EstebanValverde/Holeboard/photos/IMG_20231107_094529.jpg

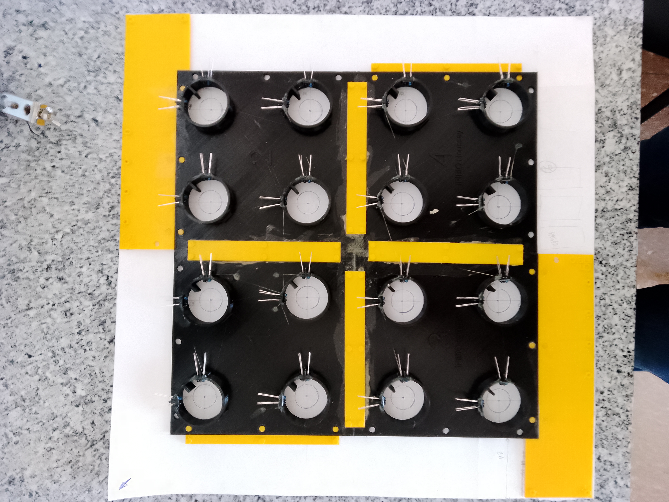
photos/IMG_20231107_094529.jpg
