EstebanValverde/Holeboard/photos/IMG_20231107_094548.jpg

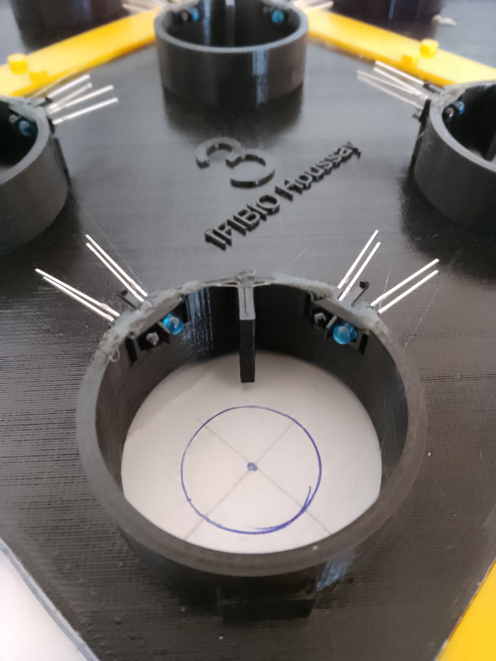
photos/IMG_20231107_094548.jpg
