EstebanValverde/Holeboard/photos/IMG_20231117_153157.jpg

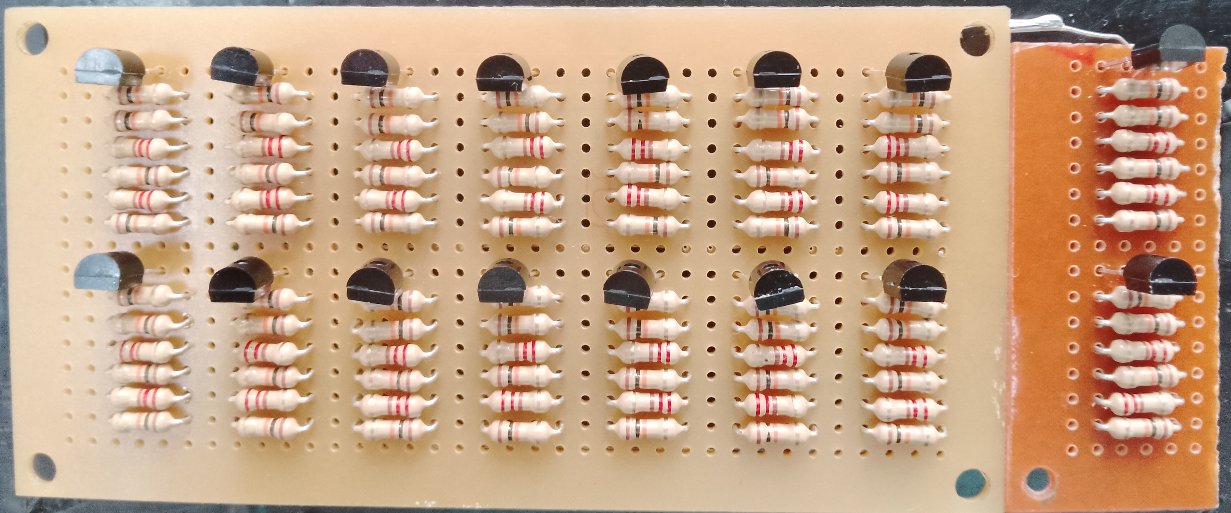
photos/IMG_20231117_153157.jpg
