EstebanValverde/Holeboard/photos/IMG_20231219_103728.jpg

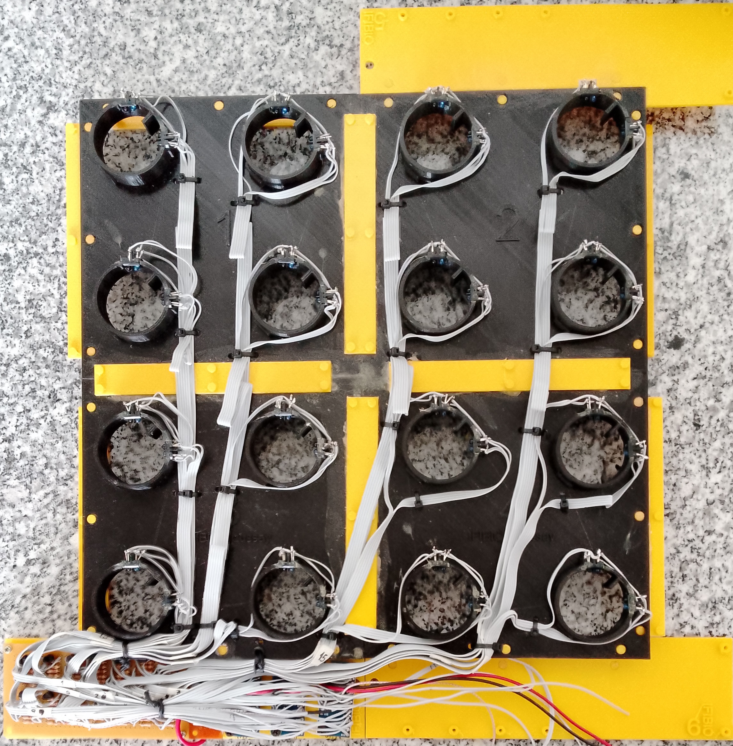
photos/IMG_20231219_103728.jpg
