EstebanValverde/Holeboard/photos/IMG_20231227_120412.jpg

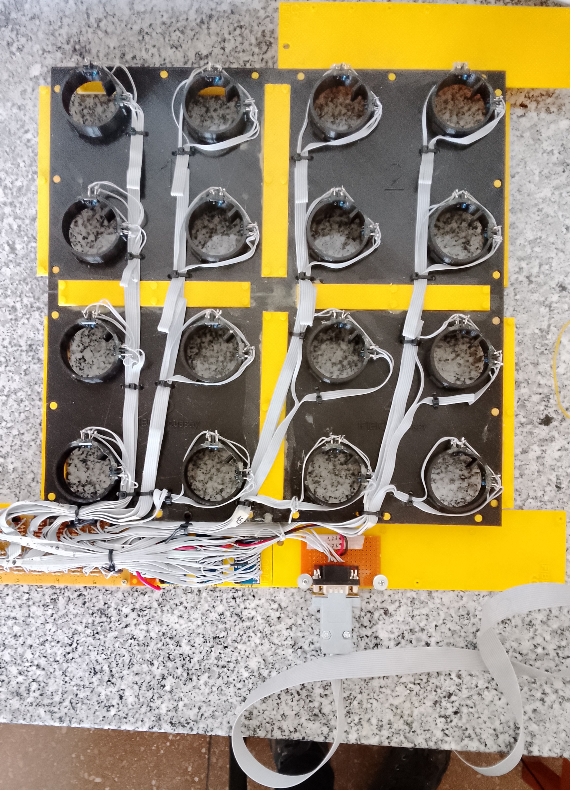
photos/IMG_20231227_120412.jpg
