EstebanValverde/Holeboard/photos/IMG_20240117_093414.jpg

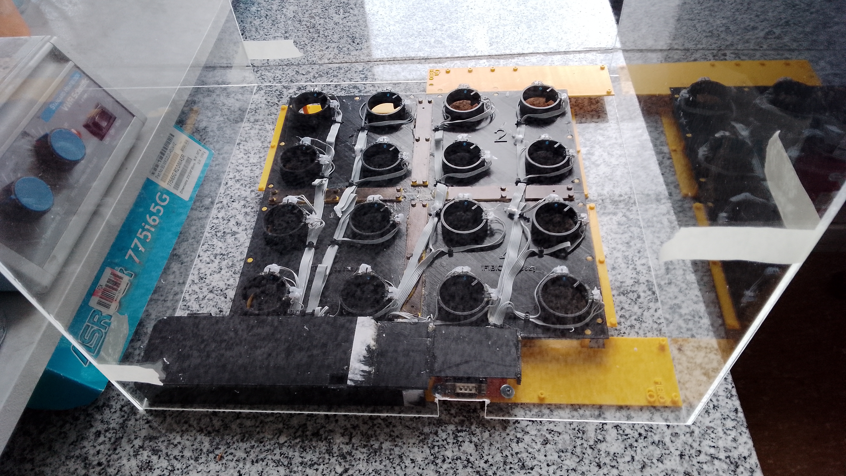
photos/IMG_20240117_093414.jpg
