EstebanValverde/Holeboard/photos/IMG_20240117_093420.jpg

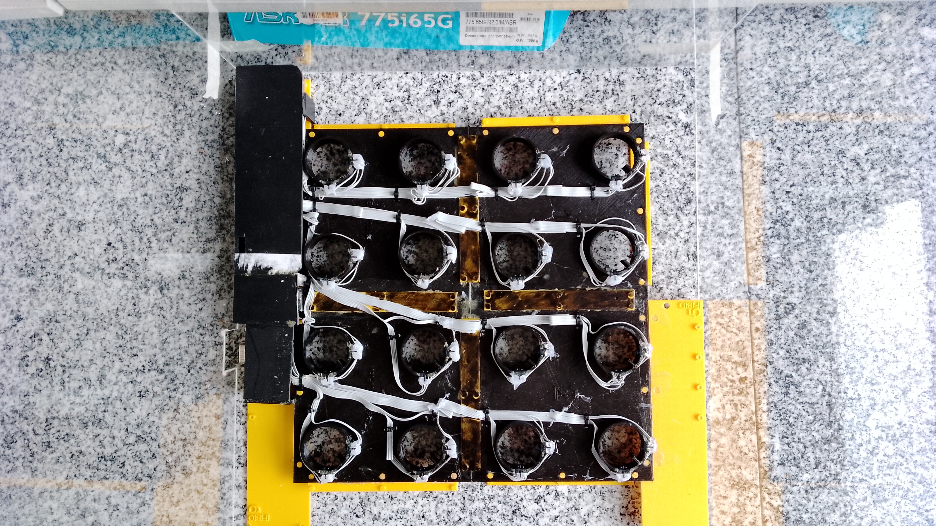
photos/IMG_20240117_093420.jpg
