EstebanValverde/Holeboard/photos/IMG_20240130_110207.jpg

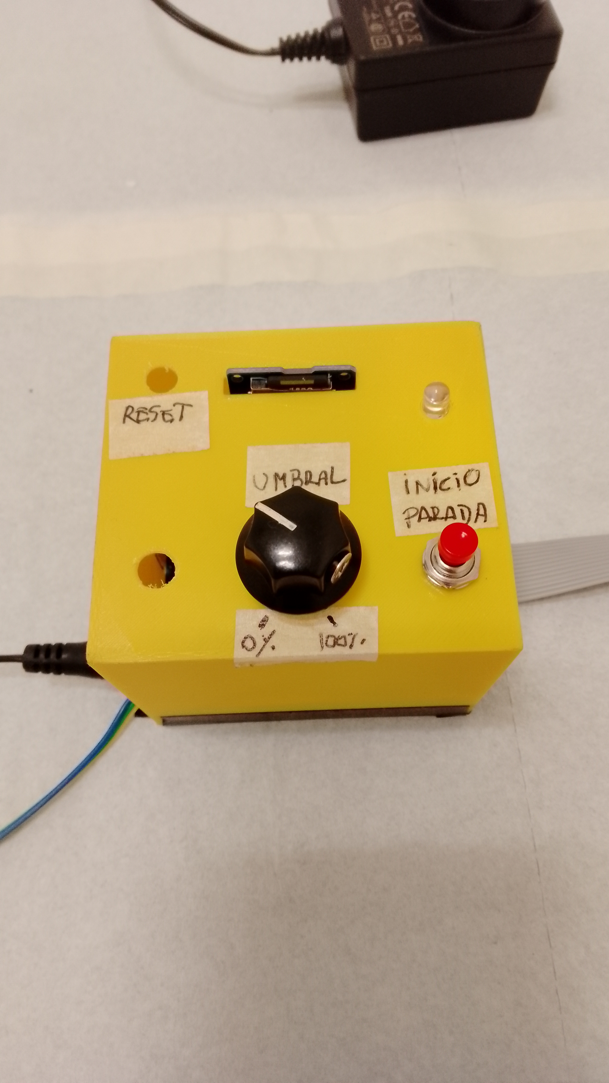
photos/IMG_20240130_110207.jpg
