EstebanValverde/Holeboard/photos/IMG_20240130_110221.jpg

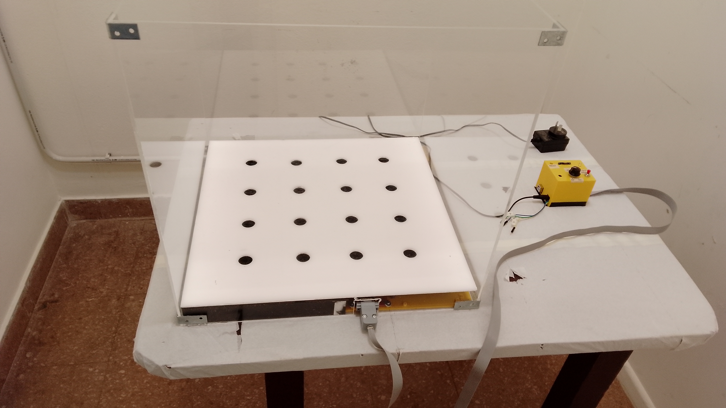
photos/IMG_20240130_110221.jpg
