EstebanValverde/Holeboard/photos/IMG_20240130_111813.jpg

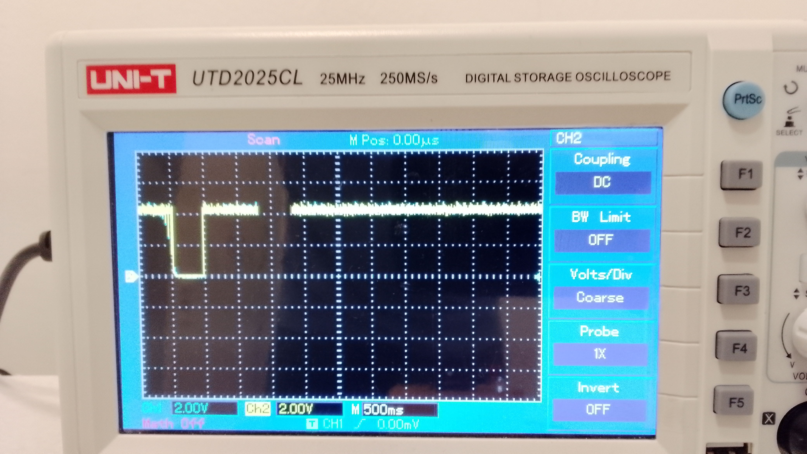
photos/IMG_20240130_111813.jpg
