EstebanValverde/Holeboard/photos/Holeboard - calibracion.jpg

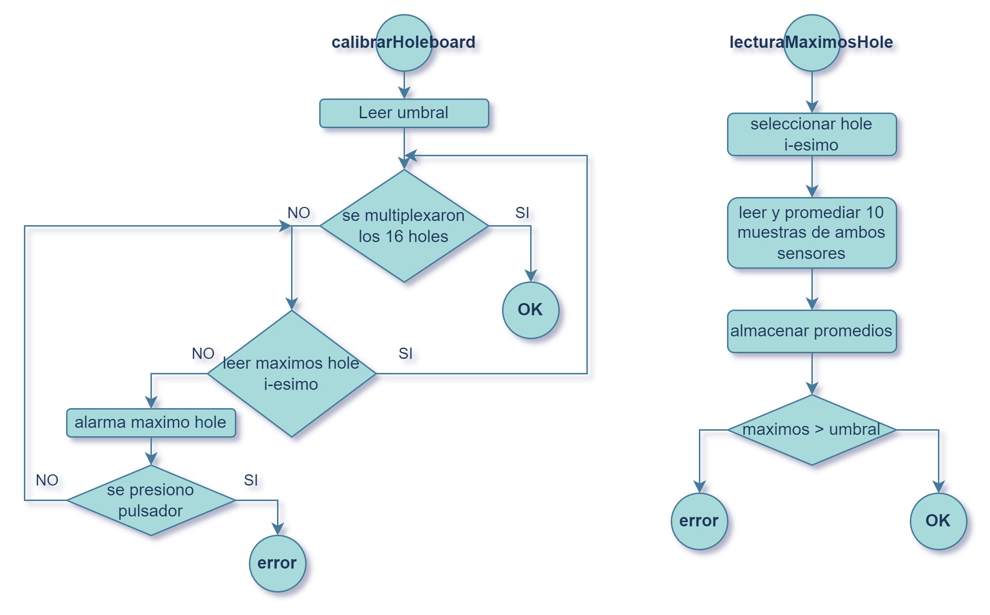
photos/Holeboard - calibracion.jpg
